BitMaker-hub/orangePill/IMAGES/IMG_20221013_171606.jpg

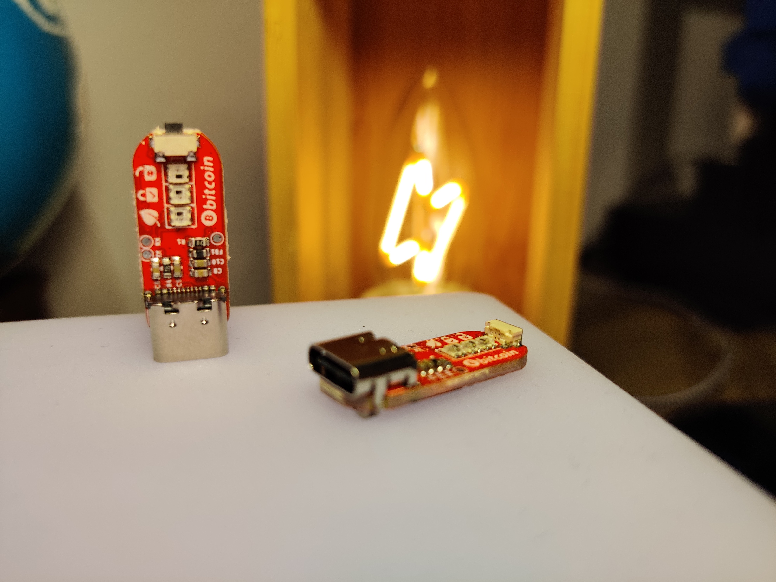
IMAGES/IMG_20221013_171606.jpg
